gelotek-com/Anki-In-Hardware/ESP32_Firmware/main/wifi_setup.cpp

#include "wifi_setup.h"

#include "freertos/FreeRTOS.h"
#include "freertos/task.h"

#include "esp_log.h"
#include "esp_wifi.h"
#include "esp_event.h"
#include "nvs_flash.h"

#include "esp_netif.h"

static const char *TAG = "WIFI";

// Credentials
static const char *ssid     = "";
static const char *password = "";

static bool wifi_connected = false;


static void wifi_event_handler(void *arg, esp_event_base_t event_base, int32_t event_id, void *event_data)
{
    if (event_base == WIFI_EVENT && event_id == WIFI_EVENT_STA_START) {
        esp_wifi_connect();
    }

    if (event_base == WIFI_EVENT && event_id == WIFI_EVENT_STA_DISCONNECTED) {
        ESP_LOGI(TAG, "Disconnected, retrying...");
        esp_wifi_connect();
        wifi_connected = false;
    }

    if (event_base == IP_EVENT && event_id == IP_EVENT_STA_GOT_IP) {
        wifi_connected = true;
        ESP_LOGI(TAG, "Got IP address");
    }
}

void setupWiFi()
{
    ESP_LOGI(TAG, "Connecting to WiFi...");

    // Initialize TCP/IP stack
    esp_netif_init();
    esp_event_loop_create_default();
    esp_netif_create_default_wifi_sta();

    // WiFi init
    wifi_init_config_t cfg = WIFI_INIT_CONFIG_DEFAULT();
    esp_wifi_init(&cfg);

    // Register event handlers
    esp_event_handler_instance_register(
        WIFI_EVENT,
        ESP_EVENT_ANY_ID,
        &wifi_event_handler,
        nullptr,
        nullptr
    );

    esp_event_handler_instance_register(
        IP_EVENT,
        IP_EVENT_STA_GOT_IP,
        &wifi_event_handler,
        nullptr,
        nullptr
    );

    // WiFi config
    wifi_config_t wifi_config = {};
    strcpy((char *)wifi_config.sta.ssid, ssid);
    strcpy((char *)wifi_config.sta.password, password);

    esp_wifi_set_mode(WIFI_MODE_STA);
    esp_wifi_set_config(WIFI_IF_STA, &wifi_config);
    esp_wifi_start();

    while (!wifi_connected) {
        ESP_LOGI(TAG, ".");
        vTaskDelay(pdMS_TO_TICKS(500));
    }

    ESP_LOGI(TAG, "Connected!");
}
